FabianGmeiner/Honda_Transalp_PD06_AuxGauge/Images/AuxGauge_Housing.jpeg

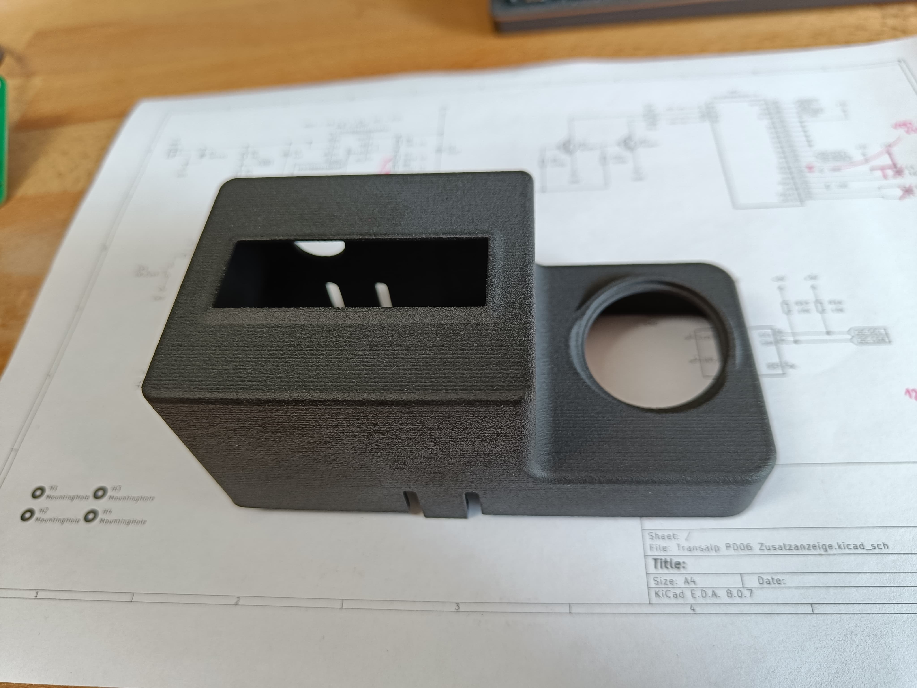
Images/AuxGauge_Housing.jpeg
