FabianGmeiner/Honda_Transalp_PD06_AuxGauge/Images/AuxGauge_Settings_6.jpeg

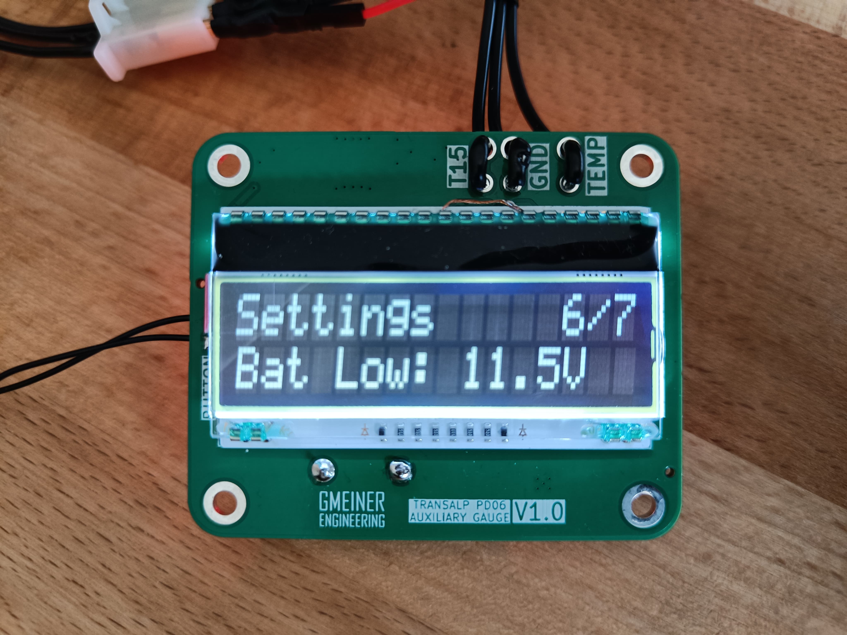
Images/AuxGauge_Settings_6.jpeg
