FabianGmeiner/Honda_Transalp_PD06_AuxGauge/Images/AuxGauge_Installed_3.jpeg

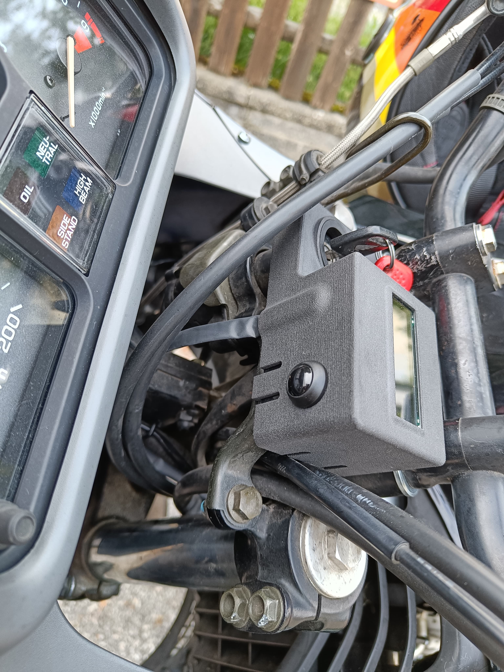
Images/AuxGauge_Installed_3.jpeg
